harryjwang/Water-Reservoir-Protection-Project/Report Files/Back_View.png

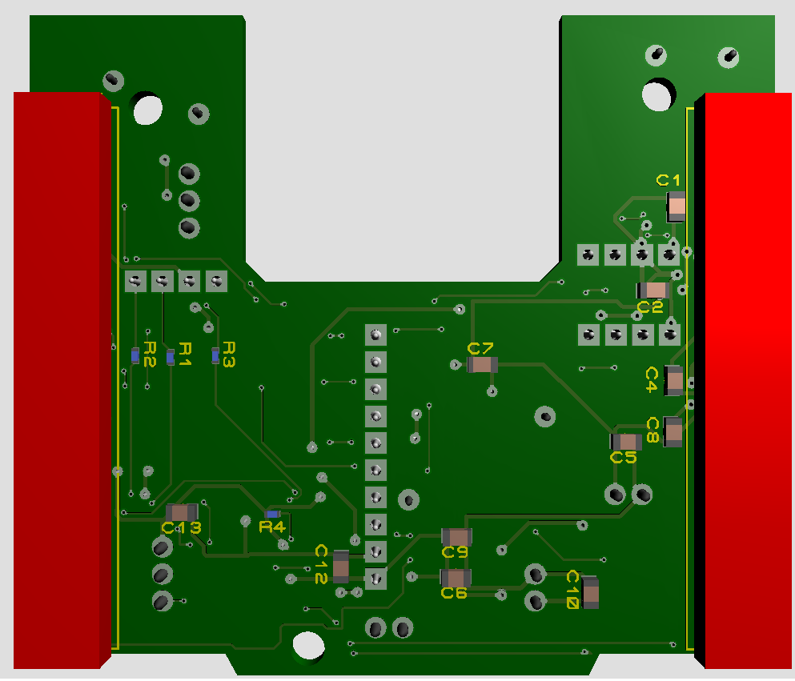
Report Files/Back_View.png
