harryjwang/Water-Reservoir-Protection-Project/Report Files/Bottom_Paste_Layer.png

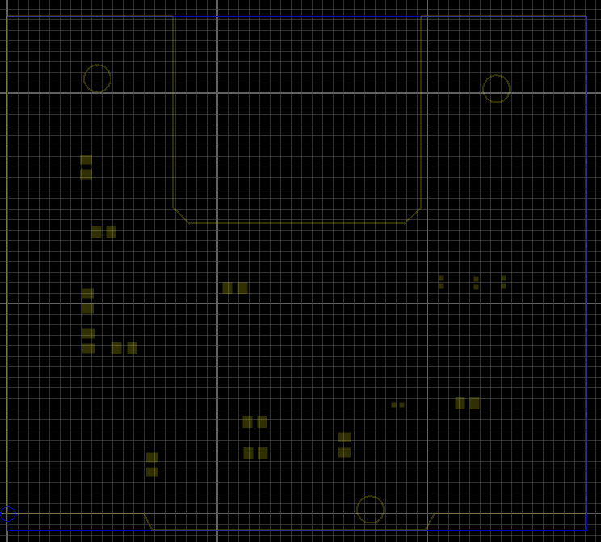
Report Files/Bottom_Paste_Layer.png
