harryjwang/Water-Reservoir-Protection-Project/Report Files/Bottom_Resistor_Layer.png

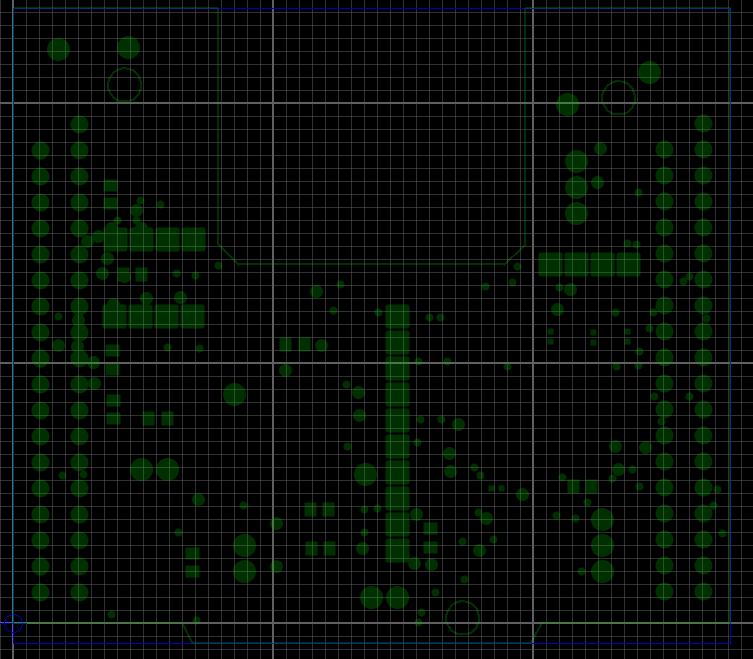
Report Files/Bottom_Resistor_Layer.png
