harryjwang/Water-Reservoir-Protection-Project/Report Files/Bottom_Silk_Layer.png

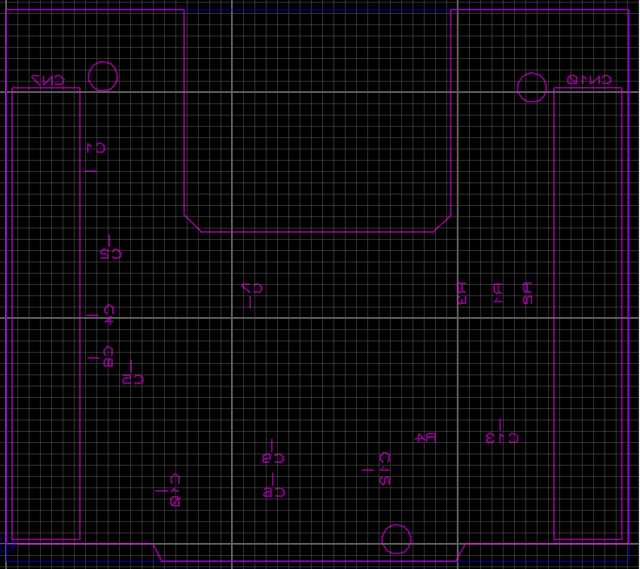
Report Files/Bottom_Silk_Layer.png
