harryjwang/Water-Reservoir-Protection-Project/Report Files/PCB_Schematic.png

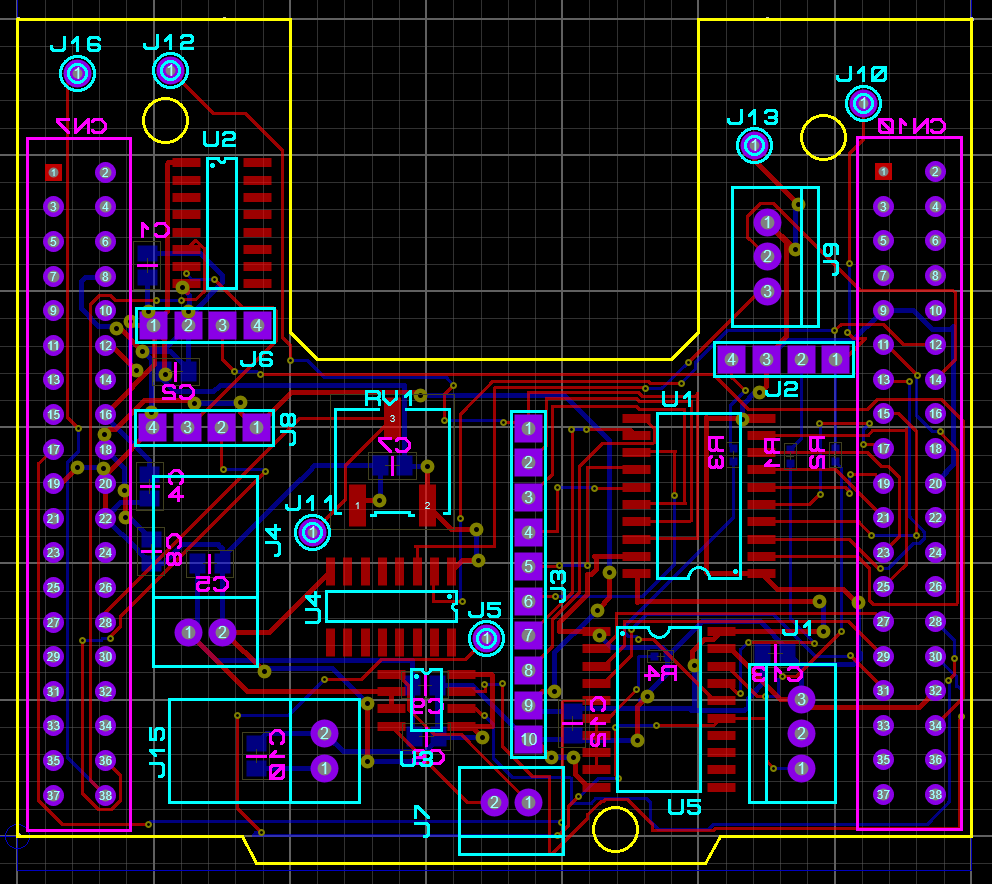
Report Files/PCB_Schematic.png
