harryjwang/Water-Reservoir-Protection-Project/Report Files/Top_Paste_Layer.png

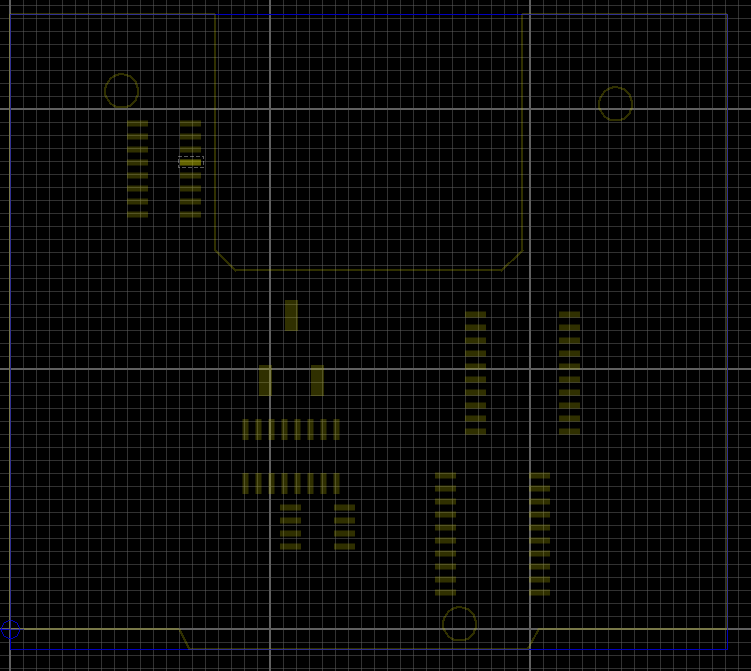
Report Files/Top_Paste_Layer.png
