harryjwang/Water-Reservoir-Protection-Project/Report Files/Top_Silk_Layer.png

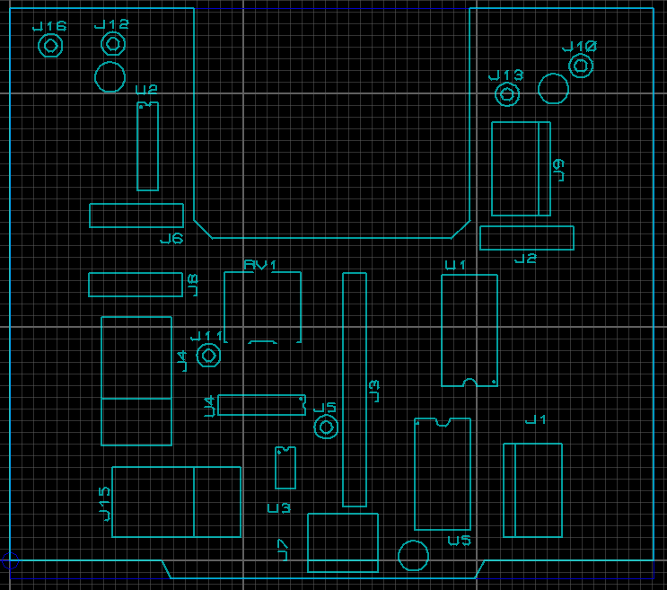
Report Files/Top_Silk_Layer.png
